yummCat/lockbox/Journal - Lockbox.md

DATE: June 4 2025  
This is going to be called a lockbox. It is a personalized safe for individuals to make sure their personal belongings are not stolen. It takes an RFID badge and a 4 digit pincode for the user to unlock the safe. The badge is a RFID wand–which is very cutesy. 



DATE: June 5 2025

Then on KiCad we had to create a schematic. It included the RFID scanner device, the key switches, the battery system, an OLED system, a reset switch, eeprom, mosfet, and boost converter to deal with components that needed 3.3V vs 5V.  
  
We added a bunch of resistors and capacitors too to make sure everybody got an appropriate current, and no components ended up fried.

DATE: June 5 2025

Then we had to create a PCB. The process involved translating the schematic into a board layout and arranging the components in a way that would fit within the available space and maintain clear routing.

We didn’t have many highly specific design constraints apart from making sure that:

- The main power supply paths were as short as possible.  
- The modules (RFID reader, EEPROM, keypad, etc.) were positioned so their connections to the microcontroller would be straightforward.  
- Decoupling capacitors were included near each IC’s power pins.

This was only our second project so we might’ve kinda winged it.



DATE: June 7 2025

Afterwards we created firmware for the lockbox. This was coded specifically for the arduino nano microcontroller. We made sure all components were accounted for in coding. This made sure that if one types the right pin \+ has the RFID wand they were able to open the door\!\!\!

Our code:  
 \#include \<Wire.h\>  
\#include \<SPI.h\>  
\#include \<MFRC522.h\>  
\#include \<Keypad.h\>

// Pin Definitions \----------  
\#define RST\_PIN        8  
\#define SS\_PIN         10  
\#define LOCK\_PIN       6  
\#define RESET\_BTN\_PIN  9

// EEPROM Definitions \----------  
\#define EEPROM\_ADDR 0x50  
\#define EEPROM\_PIN\_ADDR 0x0000

// RFID Setup \----------  
MFRC522 mfrc522(SS\_PIN, RST\_PIN);

// You can add more tags here (4-byte UIDs)  
byte validTags\[\]\[4\] \= {  
  {0xDE, 0xAD, 0xBE, 0xEF},  
  {0x12, 0x34, 0x56, 0x78}  
};  
const int numTags \= sizeof(validTags) / sizeof(validTags\[0\]);

// \---------- Keypad Setup \----------  
const byte ROES \= 3, CULS \= 3;  
char keys\[ROES\]\[CULS\] \= {  
  {'1','2','3'},  
  {'4','5','6'},  
  {'7','8','9'},  
};  
byte rowPins\[ROES\] \= {D2, D3, D4};  
byte colPins\[CULS\] \= {D5, D6, D7};  
Keypad keypad \= Keypad(makeKeymap(keys), rowPins, colPins, ROES, CULS);

// \---------- State Variables \----------  
char storedPIN\[5\] \= "0000";  
char enteredPIN\[5\];  
int pinIndex \= 0;  
unsigned long unlockTime \= 0;  
const unsigned long UNLOCK\_DURATION \= 5000;

void setup() {  
  Serial.begin(9600);  
  SPI.begin();  
  mfrc522.PCD\_Init();  
  Wire.begin();

  pinMode(LOCK\_PIN, OUTPUT);  
  pinMode(RESET\_BTN\_PIN, INPUT\_PULLUP);

  lockBox();  
  loadPINFromEEPROM();  
}

void loop() {  
  // RFID Unlock  
  if (checkRFID()) {  
    unlockBox();  
    delay(1000);  
  }

  // PIN Input  
  enteredPIN\[pinIndex\] \= '\\0';  
  char key \= keypad.getKey();  
  if (key && isDigit(key)) {  
    enteredPIN\[pinIndex++\] \= key;  
    if (pinIndex \== 4) {  
      enteredPIN\[4\] \= '\\0';  
      if (strcmp(enteredPIN, storedPIN) \== 0) {  
        unlockBox();  
      }  
      else{  
        Serial.println("Lock in brother. Wrong pin :(");  
      }  
      pinIndex \= 0;  
    }  
  }

  // Reset Button  
  if (digitalRead(RESET\_BTN\_PIN) \== LOW) {  
    delay(1000);  
    if (digitalRead(RESET\_BTN\_PIN) \== LOW) {  
      enterResetMode();  
    }  
  }

  // Auto Re-lock  
  if (digitalRead(LOCK\_PIN) \== HIGH && millis() \- unlockTime \> UNLOCK\_DURATION) {  
  lockBox();  
  }  
}

// Lock Control \----------  
void unlockBox() {  
  digitalWrite(LOCK\_PIN, HIGH);  
  unlockTime \= millis();  
  Serial.println("Unlocked\!");  
}

void lockBox() {  
  digitalWrite(LOCK\_PIN, LOW);  
}

// RFID Functions \----------  
bool checkRFID() {  
  if (\!mfrc522.PICC\_IsNewCardPresent() || \!mfrc522.PICC\_ReadCardSerial())  
    return false;

  for (int t \= 0; t \< numTags; t++) {  
    bool match \= true;  
    for (int i \= 0; i \< 4; i++) {  
      if (mfrc522.uid.uidByte\[i\] \!= validTags\[t\]\[i\]) {  
        match \= false;  
        break;  
      }  
    }  
    if (match) {  
      Serial.println("RFID matched");  
      mfrc522.PICC\_HaltA();  
      return true;  
    }  
  }  
  mfrc522.PICC\_HaltA();  
  return false;  
}

// EEPROM Functions \----------  
void savePINToEEPROM(char\* pin) {  
  Wire.beginTransmission(EEPROM\_ADDR);  
  Wire.write((EEPROM\_PIN\_ADDR \>\> 8) & 0xFF);  
  Wire.write(EEPROM\_PIN\_ADDR & 0xFF);  
  for (int i \= 0; i \< 4; i++) {  
    Wire.write(pin\[i\]);  
  }  
  Wire.endTransmission();  
  delay(10);  
  memcpy(storedPIN, pin, 5);  
}

void loadPINFromEEPROM() {  
  Wire.beginTransmission(EEPROM\_ADDR);  
  Wire.write((EEPROM\_PIN\_ADDR \>\> 8) & 0xFF);  
  Wire.write(EEPROM\_PIN\_ADDR & 0xFF);  
  Wire.endTransmission();

  Wire.requestFrom(EEPROM\_ADDR, 4);  
  for (int i \= 0; i \< 4; i++) {  
    if (Wire.available()) {  
      storedPIN\[i\] \= Wire.read();  
    }  
  }  
  storedPIN\[4\] \= '\\0';  
  Serial.print("Stored PIN: ");  
  Serial.println(storedPIN);  
}

// Reset Mode \----------  
void enterResetMode() {  
  Serial.println("Resetting PIN. Enter new 4-digit PIN:");  
  char newPIN\[5\];  
  int idx \= 0;  
  while (idx \< 4) {  
    char k \= keypad.getKey();  
    if (k && isDigit(k)) {  
      newPIN\[idx++\] \= k;  
      Serial.print('\*'); // mask entry  
    }  
  }  
  newPIN\[4\] \= '\\0';  
  savePINToEEPROM(newPIN);  
  Serial.println("\\nNew PIN saved\!");

DATE: June 10 2025

Afterwards we had to use autodesk fusion to create the full 3d model for the lockbox.

We first did the bottom. So we just created a box that was 10mm bigger on each side than the PCB and then shelled it. This created a hollow structure for the box. On the side of the box we had to create a hole for the door. So that when the user does the correct pin and has RFID the door would open(firmware helps control this). Afterwards we added ridges little rectangles protruding off of the 2 sides of the wall. These ridges are where the PCB will lie upon.



DATE: June 11 2025

Afterwards we created the top for the lockbox. We made the sides of this also be 10, larger than the sides of the PCB. We created holes for the 10 keys for the pin & created a hole for the OLED display.   
  
June 12 2025

We finally finished the 3d model by creating the door which will open with the correct criteria. This was the same size(but a little smaller on all sides) of the hole that was put on the bottom part of the case for it.  


DATE: July 7 2025

After creating the top & the bottom of the 3d case, we had to assemble all the parts together to create the full case. We did this and added a rectangle for the PCB. We made sure the rectangle was the same size of the PCB, and then put it between the top and bottom case.   


[image1]: <>

[image2]: <>

[image3]: <>

[image4]: <>

[image5]: <>

[image6]: <>

[image7]: <>
